grappendorf/homecomputer-6502/firmware/acia.h

#ifndef _ACIA_H
#define _ACIA_H

extern void acia_init();
extern void __fastcall__ acia_putc(char c);
extern void __fastcall__ acia_puts(const char * s);
extern void acia_put_newline();
extern char acia_getc();
extern void __fastcall__ acia_gets(char * buffer, unsigned char n);

#endif
